Noah1989/loopmicro/software/collapseos/doc/hw/z80/rc2014/img/acia.jpg

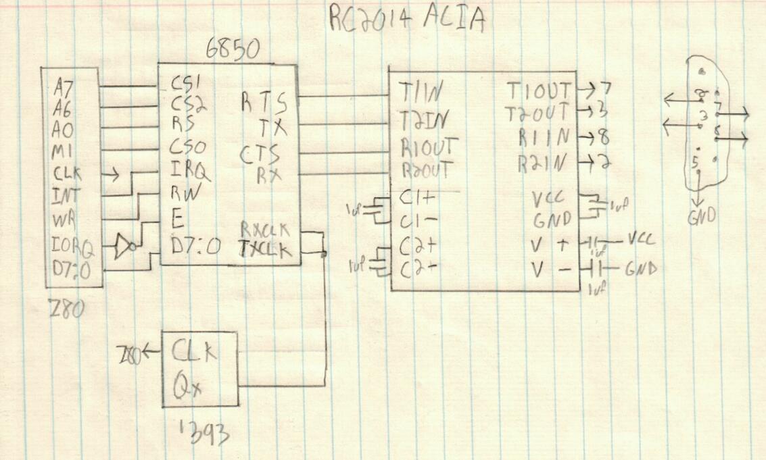
software/collapseos/doc/hw/z80/rc2014/img/acia.jpg
