Noah1989/loopmicro/memory/memory.kicad_pcb

## KiCad design memory/memory.kicad_pcb (2019-05-25)

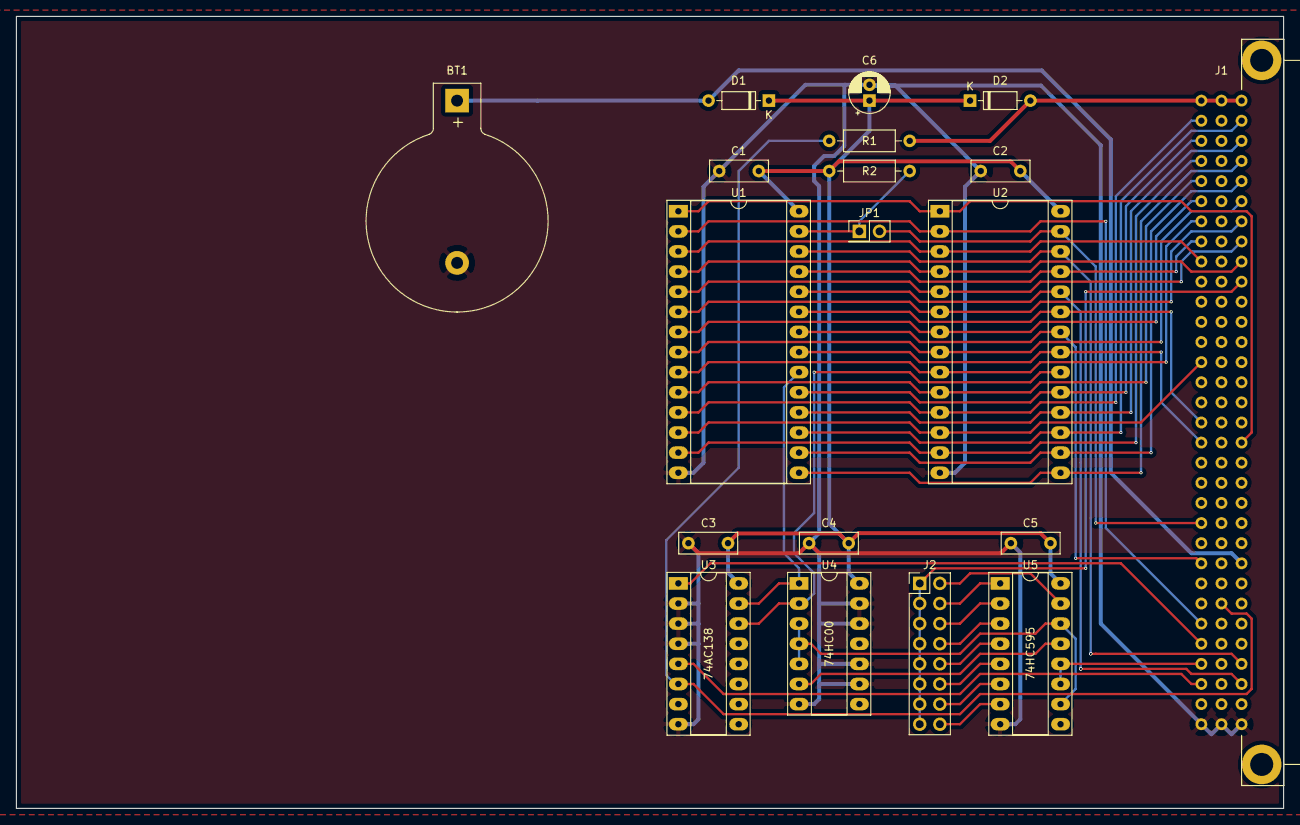
[picture p22: board memory.kicad_pcb from above]

Board: 2 copper layers, 160.0 x 100.0 mm, 19 parts (0 on the bottom side), 47 nets.

Parts:
BT1: Battery_Cell; BatteryHolder_Keystone_103_1x20mm
C1, C2, C3, C4, C5: C_Small; C_Rect_L7.2mm_W2.5mm_P5.00mm_FKS2_FKP2_MKS2_MKP2
C6: CP1; CP_Radial_D5.0mm_P2.00mm
D1, D2: D_ALT; D_DO-35_SOD27_P7.62mm_Horizontal
J1: C96ABC; Socket_DIN41612-CaseC1-full-Male-96Pin-3rows
J2: Conn_02x08_Odd_Even; PinHeader_2x08_P2.54mm_Vertical
JP1: Jumper; PinHeader_2x01_P2.54mm_Vertical
R1, R2: R; R_Axial_DIN0207_L6.3mm_D2.5mm_P10.16mm_Horizontal
U1, U2: LY62256PL-55LLI; DIP-28_W15.24mm_Socket_LongPads
U3: 74AC138; DIP-16_W7.62mm_Socket_LongPads
U4: 74HC00; DIP-14_W7.62mm_Socket_LongPads
U5: 74HC595; DIP-16_W7.62mm_Socket_LongPads

Connections:
+BATT: BT1.1, D1.2, J1.A24
A0: J1.C5, U1.10, U2.10
A1: J1.C7, U1.9, U2.9
A2: J1.A6, U1.8, U2.8
A3: J1.C6, U1.7, U2.7
A4: J1.A7, U1.6, U2.6
A5: J1.A8, U1.5, U2.5
A6: J1.A9, U1.4, U2.4
A7: J1.C9, U1.3, U2.3
A8: J1.C8, U1.25, U2.25
A9: J1.A30, U1.24, U2.24
A10: J1.C18, U1.21, U2.21
A11: J1.C17, U1.23, U2.23
A12: J1.C27, U1.2, U2.2
A13: J1.A29, U1.26, U2.26
A14: J1.A18, U1.1, U2.1
A15: J1.C28, U3.1
CLK: J1.C29, U5.11, U5.12
D0: J1.C2, U1.11, U2.11
D1: J1.C14, U1.12, U2.12
D2: J1.C4, U1.13, U2.13
D3: J1.A4, U1.15, U2.15
D4: J1.A5, U1.16, U2.16
D5: J1.A2, U1.17, U2.17
D6: J1.A3, U1.18, U2.18
D7: J1.C3, U1.19, U2.19
GND: BT1.2, C1.2, C2.2, C3.2, C4.2, C5.2, C6.2, J1.A32, J1.B32, J1.C32, U1.14, U2.14, U3.2, U3.3, U3.4, U3.8, U4.7, U4.9, U4.10, U4.12, U4.13, U5.8
unnamed: J2.2, U5.15
unnamed: J2.4, U5.1
unnamed: J2.6, U5.2
unnamed: J2.8, U5.3
unnamed: J2.10, U5.4
unnamed: J2.12, U5.5
unnamed: J2.14, U5.6
unnamed: J2.16, U5.7
unnamed: JP1.1, R2.2, U1.27
unnamed: U1.20, U3.15, U4.1
unnamed: U2.20, U3.14, U4.2
unnamed: U4.3, U4.4, U4.5, U5.10, U5.14
unnamed: U4.6, U5.13
VCC: D2.2, J1.A1, J1.B1, J1.C1, R1.2
VMEM: C1.1, C2.1, C3.1, C4.1, C5.1, C6.1, D1.1, D2.1, R2.1, U1.28, U2.28, U3.16, U4.14, U5.16
~MREQ: J1.C30, U3.5
~RD: J1.C24, U1.22, U2.22
~ROB: J1.B26, R1.1, U3.6
~WAIT: J1.A10, J2.1, J2.3, J2.5, J2.7, J2.9, J2.11, J2.13, J2.15
~WR: J1.C22, JP1.2, U2.27
