Noah1989/loopmicro/ledrom/ledrom.kicad_pcb

## KiCad design ledrom/ledrom.kicad_pcb (2019-05-25)

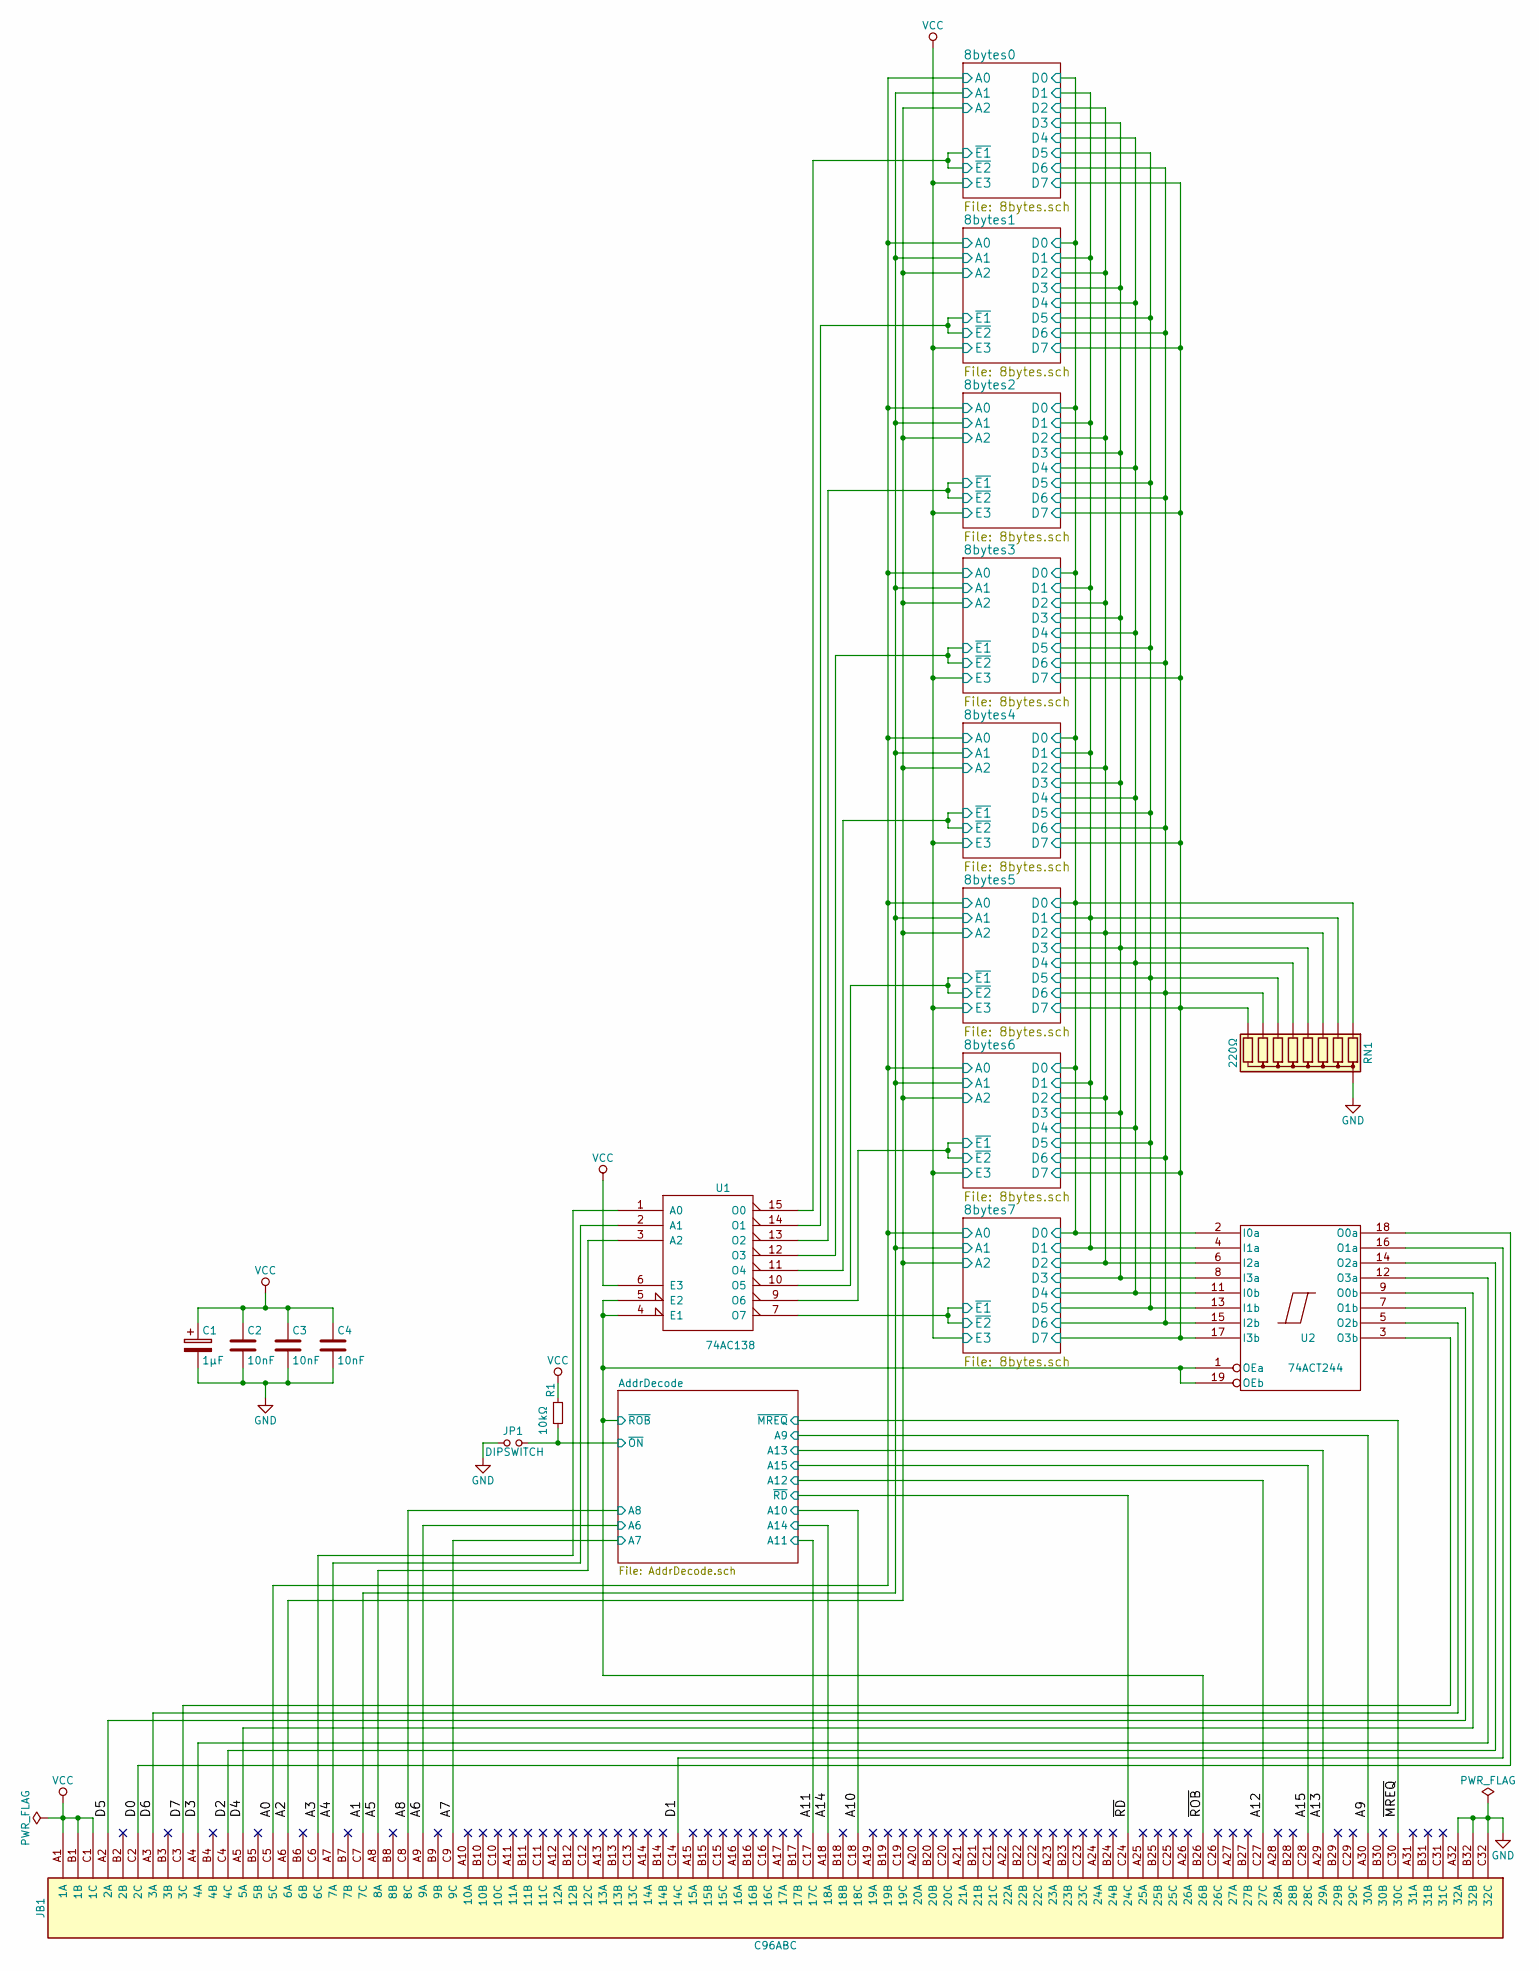
[picture p23: schematic ledrom.sch]

Parts:
C1: 1µF; CP_Radial_D5.0mm_P2.00mm
C2, C3, C4: 10nF; C_Rect_L7.0mm_W2.5mm_P5.00mm
JB1: C96ABC; Socket_DIN41612-CaseC1-full-Male-96Pin-3rows
JP1: DIPSWITCH; SW_DIP_x1_W7.62mm_Slide
R1: 10kΩ; R_Axial_DIN0207_L6.3mm_D2.5mm_P7.62mm_Horizontal
RN1: 220Ω; R_Array_SIP9
U1: 74AC138; DIP-16_W7.62mm_Socket
U2: 74ACT244; DIP-20_W7.62mm_Socket

Connections:
/8bytes0/D0: RN1.2 (R1), U2.2 (I0a); also elsewhere on the board
/8bytes0/D1: RN1.3 (R2), U2.4 (I1a); also elsewhere on the board
/8bytes0/D2: RN1.4 (R3), U2.6 (I2a); also elsewhere on the board
/8bytes0/D3: RN1.5 (R4), U2.8 (I3a); also elsewhere on the board
/8bytes0/D4: RN1.6 (R5), U2.11 (I0b); also elsewhere on the board
/8bytes0/D5: RN1.7 (R6), U2.13 (I1b); also elsewhere on the board
/8bytes0/D6: RN1.8 (R7), U2.15 (I2b); also elsewhere on the board
/8bytes0/D7: RN1.9 (R8), U2.17 (I3b); also elsewhere on the board
/8bytes0/~E1: U1.15 (O0); also elsewhere on the board
/8bytes1/~E1: U1.14 (O1); also elsewhere on the board
/8bytes2/~E1: U1.13 (O2); also elsewhere on the board
/8bytes3/~E1: U1.12 (O3); also elsewhere on the board
/8bytes4/~E1: U1.11 (O4); also elsewhere on the board
/8bytes5/~E1: U1.10 (O5); also elsewhere on the board
/8bytes6/~E1: U1.9 (O6); also elsewhere on the board
/8bytes7/~E1: U1.7 (O7); also elsewhere on the board
/A0: JB1.C5 (5C); also elsewhere on the board
/A1: JB1.C7 (7C); also elsewhere on the board
/A2: JB1.A6 (6A); also elsewhere on the board
/A3: JB1.C6 (6C), U1.1 (A0)
/A4: JB1.A7 (7A), U1.2 (A1)
/A5: JB1.A8 (8A), U1.3 (A2)
/A6: JB1.A9 (9A); also elsewhere on the board
/A7: JB1.C9 (9C); also elsewhere on the board
/A8: JB1.C8 (8C); also elsewhere on the board
/A9: JB1.A30 (30A); also elsewhere on the board
/A10: JB1.C18 (18C); also elsewhere on the board
/A11: JB1.C17 (17C); also elsewhere on the board
/A12: JB1.C27 (27C); also elsewhere on the board
/A13: JB1.A29 (29A); also elsewhere on the board
/A14: JB1.A18 (18A); also elsewhere on the board
/A15: JB1.C28 (28C); also elsewhere on the board
/AddrDecode/~ON: JP1.2, R1.2; also elsewhere on the board
/D0: JB1.C2 (2C), U2.18 (O0a)
/D1: JB1.C14 (14C), U2.16 (O1a)
/D2: JB1.C4 (4C), U2.14 (O2a)
/D3: JB1.A4 (4A), U2.12 (O3a)
/D4: JB1.A5 (5A), U2.9 (O0b)
/D5: JB1.A2 (2A), U2.7 (O1b)
/D6: JB1.A3 (3A), U2.5 (O2b)
/D7: JB1.C3 (3C), U2.3 (O3b)
/~MREQ: JB1.C30 (30C); also elsewhere on the board
/~RD: JB1.C24 (24C); also elsewhere on the board
/~ROB: JB1.B26 (26B), U1.4 (E1), U1.5 (E2), U2.1 (OEa), U2.19 (OEb); also elsewhere on the board
GND: C1.2, C2.2, C3.2, C4.2, JB1.A32 (32A), JB1.B32 (32B), JB1.C32 (32C), JP1.1, RN1.1 (common), U1.8 (GND), U2.10 (GND); also elsewhere on the board
VCC: C1.1, C2.1, C3.1, C4.1, JB1.A1 (1A), JB1.B1 (1B), JB1.C1 (1C), R1.1, U1.6 (E3), U1.16 (VCC), U2.20 (VCC); also elsewhere on the board

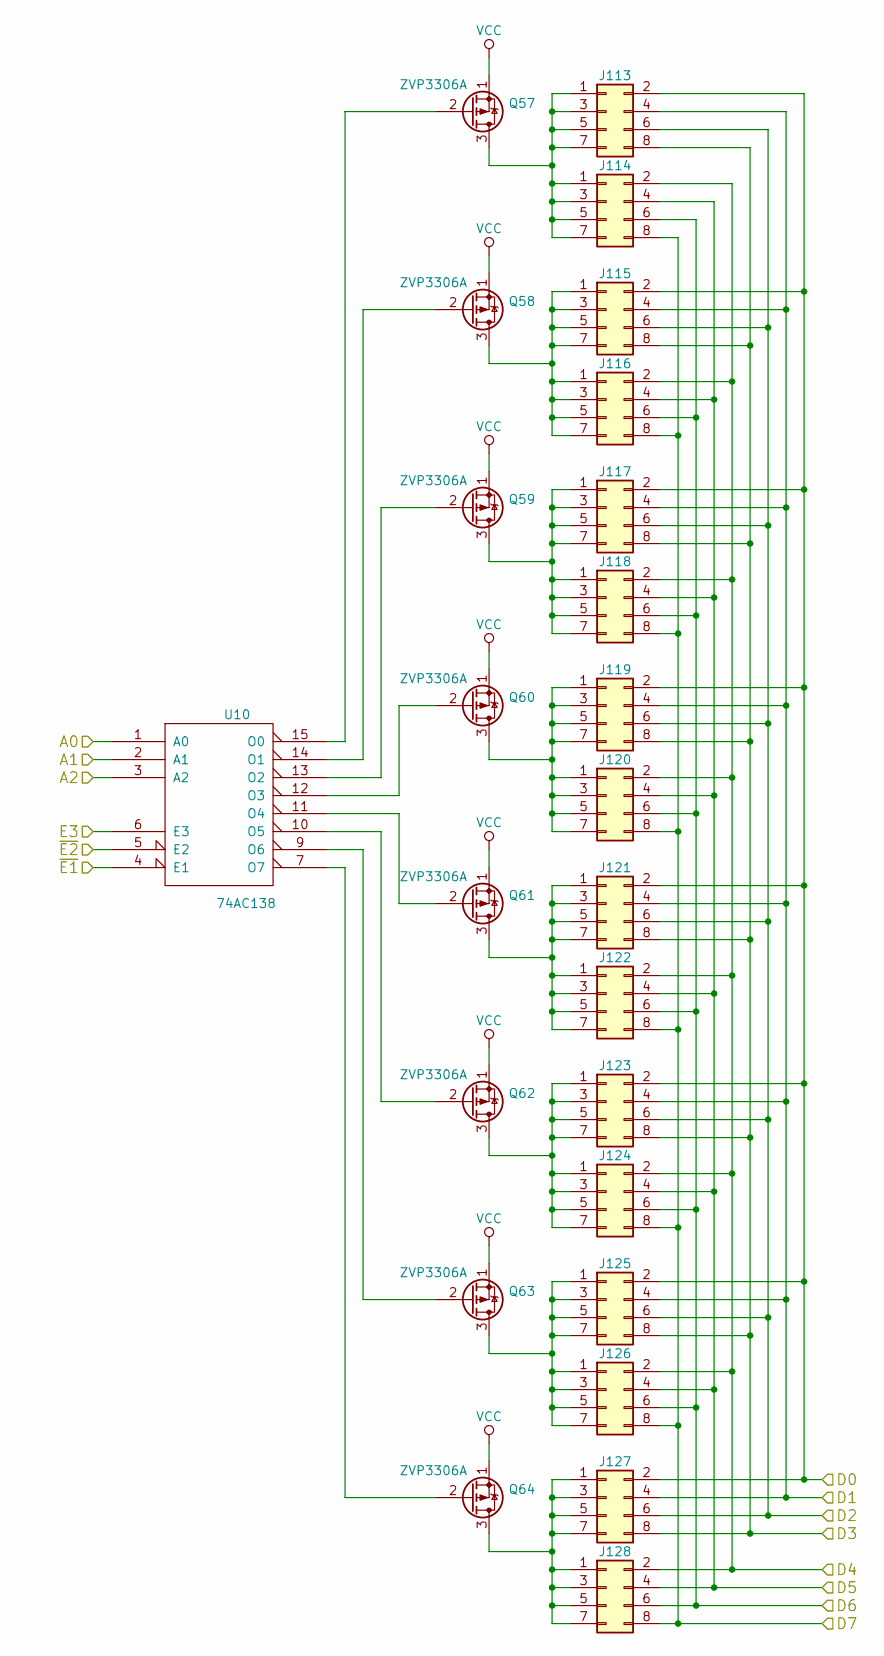
[picture p24: schematic 8bytes.sch]

Parts:
J1, J2, J3, J4, J5, J6, J7, J8, J9, J10, J11, J12, J13, J14, J15, J16: Conn_02x04_Odd_Even; Socket_Strip_Straight_2x04_Pitch2.54mm
Q1, Q2, Q3, Q4, Q5, Q6, Q7, Q8: ZVP3306A; TO-92_Inline_Narrow_Oval
U3: 74AC138; DIP-16_W7.62mm_Socket

Connections:
/8bytes0/D0: J1.2, J3.2, J5.2, J7.2, J9.2, J11.2, J13.2, J15.2; also elsewhere on the board
/8bytes0/D1: J1.4, J3.4, J5.4, J7.4, J9.4, J11.4, J13.4, J15.4; also elsewhere on the board
/8bytes0/D2: J1.6, J3.6, J5.6, J7.6, J9.6, J11.6, J13.6, J15.6; also elsewhere on the board
/8bytes0/D3: J1.8, J3.8, J5.8, J7.8, J9.8, J11.8, J13.8, J15.8; also elsewhere on the board
/8bytes0/D4: J2.2, J4.2, J6.2, J8.2, J10.2, J12.2, J14.2, J16.2; also elsewhere on the board
/8bytes0/D5: J2.4, J4.4, J6.4, J8.4, J10.4, J12.4, J14.4, J16.4; also elsewhere on the board
/8bytes0/D6: J2.6, J4.6, J6.6, J8.6, J10.6, J12.6, J14.6, J16.6; also elsewhere on the board
/8bytes0/D7: J2.8, J4.8, J6.8, J8.8, J10.8, J12.8, J14.8, J16.8; also elsewhere on the board
/8bytes0/~E1: U3.4 (E1), U3.5 (E2); also elsewhere on the board
/A0: U3.1 (A0); also elsewhere on the board
/A1: U3.2 (A1); also elsewhere on the board
/A2: U3.3 (A2); also elsewhere on the board
GND: U3.8 (GND); also elsewhere on the board
unnamed: J1.1, J1.3, J1.5, J1.7, J2.1, J2.3, J2.5, J2.7, Q1.3 (D)
unnamed: J3.1, J3.3, J3.5, J3.7, J4.1, J4.3, J4.5, J4.7, Q2.3 (D)
unnamed: J5.1, J5.3, J5.5, J5.7, J6.1, J6.3, J6.5, J6.7, Q3.3 (D)
unnamed: J7.1, J7.3, J7.5, J7.7, J8.1, J8.3, J8.5, J8.7, Q4.3 (D)
unnamed: J9.1, J9.3, J9.5, J9.7, J10.1, J10.3, J10.5, J10.7, Q5.3 (D)
unnamed: J11.1, J11.3, J11.5, J11.7, J12.1, J12.3, J12.5, J12.7, Q6.3 (D)
unnamed: J13.1, J13.3, J13.5, J13.7, J14.1, J14.3, J14.5, J14.7, Q7.3 (D)
unnamed: J15.1, J15.3, J15.5, J15.7, J16.1, J16.3, J16.5, J16.7, Q8.3 (D)
unnamed: Q1.2 (G), U3.15 (O0)
unnamed: Q2.2 (G), U3.14 (O1)
unnamed: Q3.2 (G), U3.13 (O2)
unnamed: Q4.2 (G), U3.12 (O3)
unnamed: Q5.2 (G), U3.11 (O4)
unnamed: Q6.2 (G), U3.10 (O5)
unnamed: Q7.2 (G), U3.9 (O6)
unnamed: Q8.2 (G), U3.7 (O7)
VCC: Q1.1 (S), Q2.1 (S), Q3.1 (S), Q4.1 (S), Q5.1 (S), Q6.1 (S), Q7.1 (S), Q8.1 (S), U3.6 (E3), U3.16 (VCC); also elsewhere on the board

Parts of its further copies:
J17, J18, J19, J20, J21, J22, J23, J24, J25, J26, J27, J28, J29, J30, J31, J32, J33, J34, J35, J36, J37, J38, J39, J40, J41, J42, J43, J44, J45, J46, J47, J48, J49, J50, J51, J52, J53, J54, J55, J56, J57, J58, J59, J60, J61, J62, J63, J64, J65, J66, J67, J68, J69, J70, J71, J72, J73, J74, J75, J76, J77, J78, J79, J80, J81, J82, J83, J84, J85, J86, J87, J88, J89, J90, J91, J92, J93, J94, J95, J96, J97, J98, J99, J100, J101, J102, J103, J104, J105, J106, J107, J108, J109, J110, J111, J112, J113, J114, J115, J116, J117, J118, J119, J120, J121, J122, J123, J124, J125, J126, J127, J128: Conn_02x04_Odd_Even; Socket_Strip_Straight_2x04_Pitch2.54mm
Q9, Q10, Q11, Q12, Q13, Q14, Q15, Q16, Q17, Q18, Q19, Q20, Q21, Q22, Q23, Q24, Q25, Q26, Q27, Q28, Q29, Q30, Q31, Q32, Q33, Q34, Q35, Q36, Q37, Q38, Q39, Q40, Q41, Q42, Q43, Q44, Q45, Q46, Q47, Q48, Q49, Q50, Q51, Q52, Q53, Q54, Q55, Q56, Q57, Q58, Q59, Q60, Q61, Q62, Q63, Q64: ZVP3306A; TO-92_Inline_Narrow_Oval
U4, U5, U6, U7, U8, U9, U10: 74AC138; DIP-16_W7.62mm_Socket

Connections of its further copies:
/8bytes0/D0: J17.2, J19.2, J21.2, J23.2, J25.2, J27.2, J29.2, J31.2, J33.2, J35.2, J37.2, J39.2, J41.2, J43.2, J45.2, J47.2, J49.2, J51.2, J53.2, J55.2, J57.2, J59.2, J61.2, J63.2, J65.2, J67.2, J69.2, J71.2, J73.2, J75.2, J77.2, J79.2, J81.2, J83.2, J85.2, J87.2, J89.2, J91.2, J93.2, J95.2, J97.2, J99.2, J101.2, J103.2, J105.2, J107.2, J109.2, J111.2, J113.2, J115.2, J117.2, J119.2, J121.2, J123.2, J125.2, J127.2; also elsewhere on the board
/8bytes0/D1: J17.4, J19.4, J21.4, J23.4, J25.4, J27.4, J29.4, J31.4, J33.4, J35.4, J37.4, J39.4, J41.4, J43.4, J45.4, J47.4, J49.4, J51.4, J53.4, J55.4, J57.4, J59.4, J61.4, J63.4, J65.4, J67.4, J69.4, J71.4, J73.4, J75.4, J77.4, J79.4, J81.4, J83.4, J85.4, J87.4, J89.4, J91.4, J93.4, J95.4, J97.4, J99.4, J101.4, J103.4, J105.4, J107.4, J109.4, J111.4, J113.4, J115.4, J117.4, J119.4, J121.4, J123.4, J125.4, J127.4; also elsewhere on the board
/8bytes0/D2: J17.6, J19.6, J21.6, J23.6, J25.6, J27.6, J29.6, J31.6, J33.6, J35.6, J37.6, J39.6, J41.6, J43.6, J45.6, J47.6, J49.6, J51.6, J53.6, J55.6, J57.6, J59.6, J61.6, J63.6, J65.6, J67.6, J69.6, J71.6, J73.6, J75.6, J77.6, J79.6, J81.6, J83.6, J85.6, J87.6, J89.6, J91.6, J93.6, J95.6, J97.6, J99.6, J101.6, J103.6, J105.6, J107.6, J109.6, J111.6, J113.6, J115.6, J117.6, J119.6, J121.6, J123.6, J125.6, J127.6; also elsewhere on the board
/8bytes0/D3: J17.8, J19.8, J21.8, J23.8, J25.8, J27.8, J29.8, J31.8, J33.8, J35.8, J37.8, J39.8, J41.8, J43.8, J45.8, J47.8, J49.8, J51.8, J53.8, J55.8, J57.8, J59.8, J61.8, J63.8, J65.8, J67.8, J69.8, J71.8, J73.8, J75.8, J77.8, J79.8, J81.8, J83.8, J85.8, J87.8, J89.8, J91.8, J93.8, J95.8, J97.8, J99.8, J101.8, J103.8, J105.8, J107.8, J109.8, J111.8, J113.8, J115.8, J117.8, J119.8, J121.8, J123.8, J125.8, J127.8; also elsewhere on the board
/8bytes0/D4: J18.2, J20.2, J22.2, J24.2, J26.2, J28.2, J30.2, J32.2, J34.2, J36.2, J38.2, J40.2, J42.2, J44.2, J46.2, J48.2, J50.2, J52.2, J54.2, J56.2, J58.2, J60.2, J62.2, J64.2, J66.2, J68.2, J70.2, J72.2, J74.2, J76.2, J78.2, J80.2, J82.2, J84.2, J86.2, J88.2, J90.2, J92.2, J94.2, J96.2, J98.2, J100.2, J102.2, J104.2, J106.2, J108.2, J110.2, J112.2, J114.2, J116.2, J118.2, J120.2, J122.2, J124.2, J126.2, J128.2; also elsewhere on the board
/8bytes0/D5: J18.4, J20.4, J22.4, J24.4, J26.4, J28.4, J30.4, J32.4, J34.4, J36.4, J38.4, J40.4, J42.4, J44.4, J46.4, J48.4, J50.4, J52.4, J54.4, J56.4, J58.4, J60.4, J62.4, J64.4, J66.4, J68.4, J70.4, J72.4, J74.4, J76.4, J78.4, J80.4, J82.4, J84.4, J86.4, J88.4, J90.4, J92.4, J94.4, J96.4, J98.4, J100.4, J102.4, J104.4, J106.4, J108.4, J110.4, J112.4, J114.4, J116.4, J118.4, J120.4, J122.4, J124.4, J126.4, J128.4; also elsewhere on the board
/8bytes0/D6: J18.6, J20.6, J22.6, J24.6, J26.6, J28.6, J30.6, J32.6, J34.6, J36.6, J38.6, J40.6, J42.6, J44.6, J46.6, J48.6, J50.6, J52.6, J54.6, J56.6, J58.6, J60.6, J62.6, J64.6, J66.6, J68.6, J70.6, J72.6, J74.6, J76.6, J78.6, J80.6, J82.6, J84.6, J86.6, J88.6, J90.6, J92.6, J94.6, J96.6, J98.6, J100.6, J102.6, J104.6, J106.6, J108.6, J110.6, J112.6, J114.6, J116.6, J118.6, J120.6, J122.6, J124.6, J126.6, J128.6; also elsewhere on the board
/8bytes0/D7: J18.8, J20.8, J22.8, J24.8, J26.8, J28.8, J30.8, J32.8, J34.8, J36.8, J38.8, J40.8, J42.8, J44.8, J46.8, J48.8, J50.8, J52.8, J54.8, J56.8, J58.8, J60.8, J62.8, J64.8, J66.8, J68.8, J70.8, J72.8, J74.8, J76.8, J78.8, J80.8, J82.8, J84.8, J86.8, J88.8, J90.8, J92.8, J94.8, J96.8, J98.8, J100.8, J102.8, J104.8, J106.8, J108.8, J110.8, J112.8, J114.8, J116.8, J118.8, J120.8, J122.8, J124.8, J126.8, J128.8; also elsewhere on the board
/8bytes1/~E1: U4.4 (E1), U4.5 (E2); also elsewhere on the board
/8bytes2/~E1: U5.4 (E1), U5.5 (E2); also elsewhere on the board
/8bytes3/~E1: U6.4 (E1), U6.5 (E2); also elsewhere on the board
/8bytes4/~E1: U7.4 (E1), U7.5 (E2); also elsewhere on the board
/8bytes5/~E1: U8.4 (E1), U8.5 (E2); also elsewhere on the board
/8bytes6/~E1: U9.4 (E1), U9.5 (E2); also elsewhere on the board
/8bytes7/~E1: U10.4 (E1), U10.5 (E2); also elsewhere on the board
/A0: U4.1 (A0), U5.1 (A0), U6.1 (A0), U7.1 (A0), U8.1 (A0), U9.1 (A0), U10.1 (A0); also elsewhere on the board
/A1: U4.2 (A1), U5.2 (A1), U6.2 (A1), U7.2 (A1), U8.2 (A1), U9.2 (A1), U10.2 (A1); also elsewhere on the board
/A2: U4.3 (A2), U5.3 (A2), U6.3 (A2), U7.3 (A2), U8.3 (A2), U9.3 (A2), U10.3 (A2); also elsewhere on the board
GND: U4.8 (GND), U5.8 (GND), U6.8 (GND), U7.8 (GND), U8.8 (GND), U9.8 (GND), U10.8 (GND); also elsewhere on the board
unnamed: J17.1, J17.3, J17.5, J17.7, J18.1, J18.3, J18.5, J18.7, Q9.3 (D)
unnamed: J19.1, J19.3, J19.5, J19.7, J20.1, J20.3, J20.5, J20.7, Q10.3 (D)
unnamed: J21.1, J21.3, J21.5, J21.7, J22.1, J22.3, J22.5, J22.7, Q11.3 (D)
unnamed: J23.1, J23.3, J23.5, J23.7, J24.1, J24.3, J24.5, J24.7, Q12.3 (D)
unnamed: J25.1, J25.3, J25.5, J25.7, J26.1, J26.3, J26.5, J26.7, Q13.3 (D)
unnamed: J27.1, J27.3, J27.5, J27.7, J28.1, J28.3, J28.5, J28.7, Q14.3 (D)
unnamed: J29.1, J29.3, J29.5, J29.7, J30.1, J30.3, J30.5, J30.7, Q15.3 (D)
unnamed: J31.1, J31.3, J31.5, J31.7, J32.1, J32.3, J32.5, J32.7, Q16.3 (D)
unnamed: J33.1, J33.3, J33.5, J33.7, J34.1, J34.3, J34.5, J34.7, Q17.3 (D)
unnamed: J35.1, J35.3, J35.5, J35.7, J36.1, J36.3, J36.5, J36.7, Q18.3 (D)
unnamed: J37.1, J37.3, J37.5, J37.7, J38.1, J38.3, J38.5, J38.7, Q19.3 (D)
unnamed: J39.1, J39.3, J39.5, J39.7, J40.1, J40.3, J40.5, J40.7, Q20.3 (D)
unnamed: J41.1, J41.3, J41.5, J41.7, J42.1, J42.3, J42.5, J42.7, Q21.3 (D)
unnamed: J43.1, J43.3, J43.5, J43.7, J44.1, J44.3, J44.5, J44.7, Q22.3 (D)
unnamed: J45.1, J45.3, J45.5, J45.7, J46.1, J46.3, J46.5, J46.7, Q23.3 (D)
unnamed: J47.1, J47.3, J47.5, J47.7, J48.1, J48.3, J48.5, J48.7, Q24.3 (D)
unnamed: J49.1, J49.3, J49.5, J49.7, J50.1, J50.3, J50.5, J50.7, Q25.3 (D)
unnamed: J51.1, J51.3, J51.5, J51.7, J52.1, J52.3, J52.5, J52.7, Q26.3 (D)
unnamed: J53.1, J53.3, J53.5, J53.7, J54.1, J54.3, J54.5, J54.7, Q27.3 (D)
unnamed: J55.1, J55.3, J55.5, J55.7, J56.1, J56.3, J56.5, J56.7, Q28.3 (D)
unnamed: J57.1, J57.3, J57.5, J57.7, J58.1, J58.3, J58.5, J58.7, Q29.3 (D)
unnamed: J59.1, J59.3, J59.5, J59.7, J60.1, J60.3, J60.5, J60.7, Q30.3 (D)
unnamed: J61.1, J61.3, J61.5, J61.7, J62.1, J62.3, J62.5, J62.7, Q31.3 (D)
unnamed: J63.1, J63.3, J63.5, J63.7, J64.1, J64.3, J64.5, J64.7, Q32.3 (D)
unnamed: J65.1, J65.3, J65.5, J65.7, J66.1, J66.3, J66.5, J66.7, Q33.3 (D)
unnamed: J67.1, J67.3, J67.5, J67.7, J68.1, J68.3, J68.5, J68.7, Q34.3 (D)
unnamed: J69.1, J69.3, J69.5, J69.7, J70.1, J70.3, J70.5, J70.7, Q35.3 (D)
unnamed: J71.1, J71.3, J71.5, J71.7, J72.1, J72.3, J72.5, J72.7, Q36.3 (D)
unnamed: J73.1, J73.3, J73.5, J73.7, J74.1, J74.3, J74.5, J74.7, Q37.3 (D)
unnamed: J75.1, J75.3, J75.5, J75.7, J76.1, J76.3, J76.5, J76.7, Q38.3 (D)
unnamed: J77.1, J77.3, J77.5, J77.7, J78.1, J78.3, J78.5, J78.7, Q39.3 (D)
unnamed: J79.1, J79.3, J79.5, J79.7, J80.1, J80.3, J80.5, J80.7, Q40.3 (D)
unnamed: J81.1, J81.3, J81.5, J81.7, J82.1, J82.3, J82.5, J82.7, Q41.3 (D)
unnamed: J83.1, J83.3, J83.5, J83.7, J84.1, J84.3, J84.5, J84.7, Q42.3 (D)
unnamed: J85.1, J85.3, J85.5, J85.7, J86.1, J86.3, J86.5, J86.7, Q43.3 (D)
unnamed: J87.1, J87.3, J87.5, J87.7, J88.1, J88.3, J88.5, J88.7, Q44.3 (D)
unnamed: J89.1, J89.3, J89.5, J89.7, J90.1, J90.3, J90.5, J90.7, Q45.3 (D)
unnamed: J91.1, J91.3, J91.5, J91.7, J92.1, J92.3, J92.5, J92.7, Q46.3 (D)
unnamed: J93.1, J93.3, J93.5, J93.7, J94.1, J94.3, J94.5, J94.7, Q47.3 (D)
unnamed: J95.1, J95.3, J95.5, J95.7, J96.1, J96.3, J96.5, J96.7, Q48.3 (D)
unnamed: J97.1, J97.3, J97.5, J97.7, J98.1, J98.3, J98.5, J98.7, Q49.3 (D)
unnamed: J99.1, J99.3, J99.5, J99.7, J100.1, J100.3, J100.5, J100.7, Q50.3 (D)
unnamed: J101.1, J101.3, J101.5, J101.7, J102.1, J102.3, J102.5, J102.7, Q51.3 (D)
unnamed: J103.1, J103.3, J103.5, J103.7, J104.1, J104.3, J104.5, J104.7, Q52.3 (D)
unnamed: J105.1, J105.3, J105.5, J105.7, J106.1, J106.3, J106.5, J106.7, Q53.3 (D)
unnamed: J107.1, J107.3, J107.5, J107.7, J108.1, J108.3, J108.5, J108.7, Q54.3 (D)
unnamed: J109.1, J109.3, J109.5, J109.7, J110.1, J110.3, J110.5, J110.7, Q55.3 (D)
unnamed: J111.1, J111.3, J111.5, J111.7, J112.1, J112.3, J112.5, J112.7, Q56.3 (D)
unnamed: J113.1, J113.3, J113.5, J113.7, J114.1, J114.3, J114.5, J114.7, Q57.3 (D)
unnamed: J115.1, J115.3, J115.5, J115.7, J116.1, J116.3, J116.5, J116.7, Q58.3 (D)
unnamed: J117.1, J117.3, J117.5, J117.7, J118.1, J118.3, J118.5, J118.7, Q59.3 (D)
unnamed: J119.1, J119.3, J119.5, J119.7, J120.1, J120.3, J120.5, J120.7, Q60.3 (D)
unnamed: J121.1, J121.3, J121.5, J121.7, J122.1, J122.3, J122.5, J122.7, Q61.3 (D)
unnamed: J123.1, J123.3, J123.5, J123.7, J124.1, J124.3, J124.5, J124.7, Q62.3 (D)
unnamed: J125.1, J125.3, J125.5, J125.7, J126.1, J126.3, J126.5, J126.7, Q63.3 (D)
unnamed: J127.1, J127.3, J127.5, J127.7, J128.1, J128.3, J128.5, J128.7, Q64.3 (D)
unnamed: Q9.2 (G), U4.15 (O0)
unnamed: Q10.2 (G), U4.14 (O1)
unnamed: Q11.2 (G), U4.13 (O2)
unnamed: Q12.2 (G), U4.12 (O3)
unnamed: Q13.2 (G), U4.11 (O4)
unnamed: Q14.2 (G), U4.10 (O5)
unnamed: Q15.2 (G), U4.9 (O6)
unnamed: Q16.2 (G), U4.7 (O7)
unnamed: Q17.2 (G), U5.15 (O0)
unnamed: Q18.2 (G), U5.14 (O1)
unnamed: Q19.2 (G), U5.13 (O2)
unnamed: Q20.2 (G), U5.12 (O3)
unnamed: Q21.2 (G), U5.11 (O4)
unnamed: Q22.2 (G), U5.10 (O5)
unnamed: Q23.2 (G), U5.9 (O6)
unnamed: Q24.2 (G), U5.7 (O7)
unnamed: Q25.2 (G), U6.15 (O0)
unnamed: Q26.2 (G), U6.14 (O1)
unnamed: Q27.2 (G), U6.13 (O2)
unnamed: Q28.2 (G), U6.12 (O3)
unnamed: Q29.2 (G), U6.11 (O4)
unnamed: Q30.2 (G), U6.10 (O5)
unnamed: Q31.2 (G), U6.9 (O6)
unnamed: Q32.2 (G), U6.7 (O7)
unnamed: Q33.2 (G), U7.15 (O0)
unnamed: Q34.2 (G), U7.14 (O1)
unnamed: Q35.2 (G), U7.13 (O2)
unnamed: Q36.2 (G), U7.12 (O3)
unnamed: Q37.2 (G), U7.11 (O4)
unnamed: Q38.2 (G), U7.10 (O5)
unnamed: Q39.2 (G), U7.9 (O6)
unnamed: Q40.2 (G), U7.7 (O7)
unnamed: Q41.2 (G), U8.15 (O0)
unnamed: Q42.2 (G), U8.14 (O1)
unnamed: Q43.2 (G), U8.13 (O2)
unnamed: Q44.2 (G), U8.12 (O3)
unnamed: Q45.2 (G), U8.11 (O4)
unnamed: Q46.2 (G), U8.10 (O5)
unnamed: Q47.2 (G), U8.9 (O6)
unnamed: Q48.2 (G), U8.7 (O7)
unnamed: Q49.2 (G), U9.15 (O0)
unnamed: Q50.2 (G), U9.14 (O1)
unnamed: Q51.2 (G), U9.13 (O2)
unnamed: Q52.2 (G), U9.12 (O3)
unnamed: Q53.2 (G), U9.11 (O4)
unnamed: Q54.2 (G), U9.10 (O5)
unnamed: Q55.2 (G), U9.9 (O6)
unnamed: Q56.2 (G), U9.7 (O7)
unnamed: Q57.2 (G), U10.15 (O0)
unnamed: Q58.2 (G), U10.14 (O1)
unnamed: Q59.2 (G), U10.13 (O2)
unnamed: Q60.2 (G), U10.12 (O3)
unnamed: Q61.2 (G), U10.11 (O4)
unnamed: Q62.2 (G), U10.10 (O5)
unnamed: Q63.2 (G), U10.9 (O6)
unnamed: Q64.2 (G), U10.7 (O7)
VCC: Q9.1 (S), Q10.1 (S), Q11.1 (S), Q12.1 (S), Q13.1 (S), Q14.1 (S), Q15.1 (S), Q16.1 (S), Q17.1 (S), Q18.1 (S), Q19.1 (S), Q20.1 (S), Q21.1 (S), Q22.1 (S), Q23.1 (S), Q24.1 (S), Q25.1 (S), Q26.1 (S), Q27.1 (S), Q28.1 (S), Q29.1 (S), Q30.1 (S), Q31.1 (S), Q32.1 (S), Q33.1 (S), Q34.1 (S), Q35.1 (S), Q36.1 (S), Q37.1 (S), Q38.1 (S), Q39.1 (S), Q40.1 (S), Q41.1 (S), Q42.1 (S), Q43.1 (S), Q44.1 (S), Q45.1 (S), Q46.1 (S), Q47.1 (S), Q48.1 (S), Q49.1 (S), Q50.1 (S), Q51.1 (S), Q52.1 (S), Q53.1 (S), Q54.1 (S), Q55.1 (S), Q56.1 (S), Q57.1 (S), Q58.1 (S), Q59.1 (S), Q60.1 (S), Q61.1 (S), Q62.1 (S), Q63.1 (S), Q64.1 (S), U4.6 (E3), U4.16 (VCC), U5.6 (E3), U5.16 (VCC), U6.6 (E3), U6.16 (VCC), U7.6 (E3), U7.16 (VCC), U8.6 (E3), U8.16 (VCC), U9.6 (E3), U9.16 (VCC), U10.6 (E3), U10.16 (VCC); also elsewhere on the board

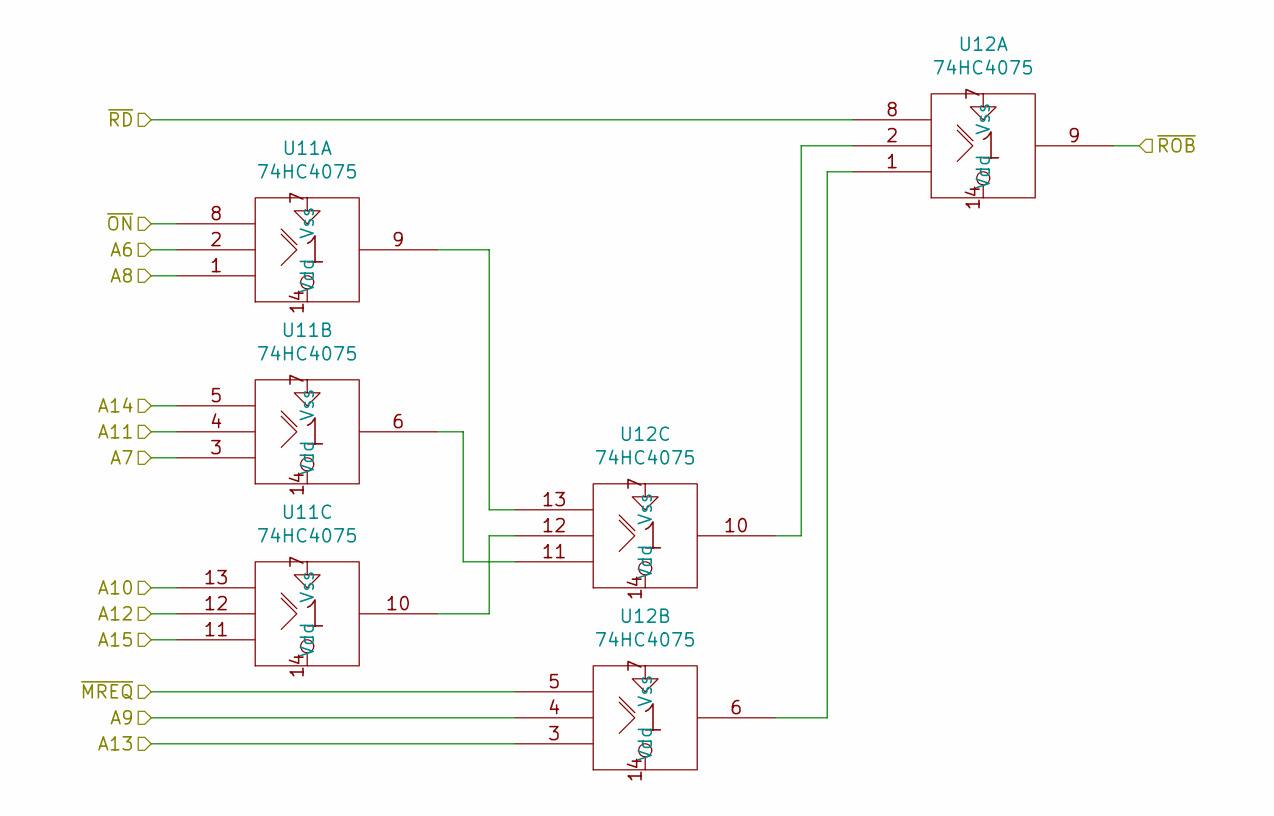
[picture p25: schematic AddrDecode.sch]

Parts:
U11, U12: 74HC4075; DIP-14_W7.62mm_Socket

Connections:
/A6: U11.2; also elsewhere on the board
/A7: U11.3; also elsewhere on the board
/A8: U11.1; also elsewhere on the board
/A9: U12.4; also elsewhere on the board
/A10: U11.13; also elsewhere on the board
/A11: U11.4; also elsewhere on the board
/A12: U11.12; also elsewhere on the board
/A13: U12.3; also elsewhere on the board
/A14: U11.5; also elsewhere on the board
/A15: U11.11; also elsewhere on the board
/AddrDecode/~ON: U11.8; also elsewhere on the board
/~MREQ: U12.5; also elsewhere on the board
/~RD: U12.8; also elsewhere on the board
/~ROB: U12.9; also elsewhere on the board
GND: U11.7 (Vss), U12.7 (Vss); also elsewhere on the board
unnamed: U11.6, U12.11
unnamed: U11.9, U12.13
unnamed: U11.10, U12.12
unnamed: U12.1, U12.6
unnamed: U12.2, U12.10
VCC: U11.14 (Vdd), U12.14 (Vdd); also elsewhere on the board

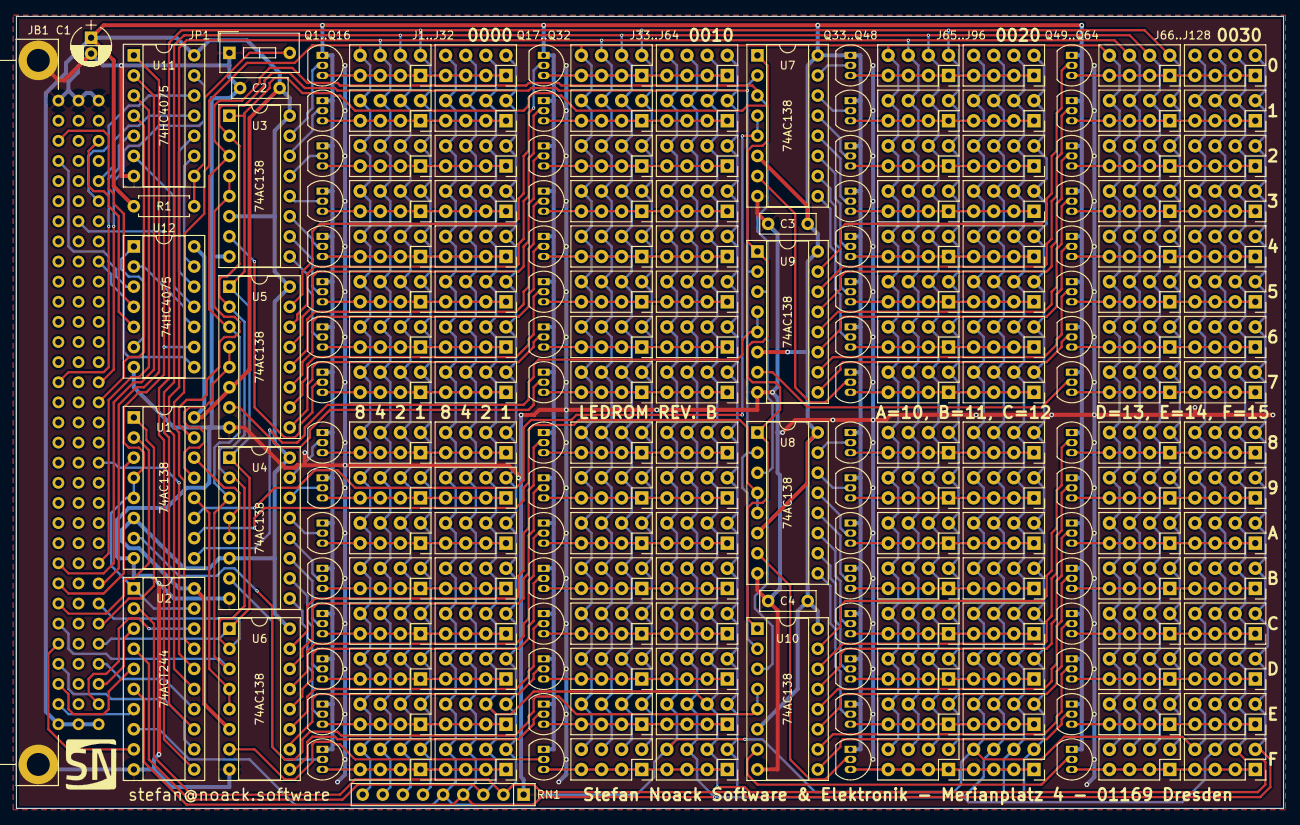
[picture p26: board ledrom.kicad_pcb from above]

Board: 2 copper layers, 160.0 x 100.0 mm, 212 parts (0 on the bottom side), 179 nets.
