Noah1989/loopmicro/software/new-rom/fat32.asm

public fat32_init
public fat32_working_directory
public fat32_fat_begin_lba
public fat32_fat_number_of_sectors
public fat32_chain_IX_get_byte_A
public fat32_chain_IX_put_byte_A
public fat32_chain_IX_skip_bytes_BC
public fat32_chain_IX_seek_BCDE


extern sdcard_read_block_DEHL_lazy
extern sdcard_block_buffer
extern sdcard_current_block_address
extern sdcard_current_block_dirty

extern stream_IX_seek_BCDE
extern stream_IX_read_block_DE_len_BC_bytewise
extern stream_IX_write_block_DE_len_BC_bytewise

extern debug_io_print_character_A
extern debug_io_print_hex_byte_A
extern error

include "stream.inc"
include "fat32.inc"

defc volumeid_bytes_per_sector      = $00B ; ds.b 2
defc volumeid_sectors_per_cluster   = $00D ; ds.b 1
defc volumeid_reserved_sectors      = $00E ; ds.b 2
defc volumeid_number_of_fats        = $010 ; ds.b 1
defc volumeid_sectors_per_fat       = $024 ; ds.b 4
defc volumeid_rootdir_first_cluster = $02C ; ds.b 4
defc volumeid_signature             = $1FE ; ds.b 2

fat32_init:
	; read master boot record
	LD	DE, 0
	LD	HL, 0
	CALL	sdcard_read_block_DEHL_lazy
	; verify this is a dos mbr
	LD	HL, (sdcard_block_buffer+mbr_magic)
	LD	BC, $AA55
	AND	A, A
	SBC	HL, BC
fat32_init_error_invalid_mbr_signature:
	CALL	NZ, error
	; verify filesystem type is $0B or $0C (FAT32)
	LD	A, (sdcard_block_buffer+mbr_partition_1+partition_type_code)
	CP	A, $0B
	JR	Z, fat32_init_type_ok
	CP	A, $0C
fat32_init_error_invalid_fs_type:
	CALL	NZ, error
fat32_init_type_ok:
	; read volume id
	LD	HL, (sdcard_block_buffer+mbr_partition_1+partition_lba_begin)
	LD	DE, (sdcard_block_buffer+mbr_partition_1+partition_lba_begin+2)
	CALL	sdcard_read_block_DEHL_lazy
	; check signature
	LD	HL, (sdcard_block_buffer+volumeid_signature)
	LD	BC, $AA55
	AND	A, A
	SBC	HL, BC
fat32_init_error_invalid_volumeid_signature:
	CALL	NZ, error
	; check bytes per sector
	LD	HL, (sdcard_block_buffer+volumeid_bytes_per_sector)
	LD	BC, 512
	AND	A, A
	SBC	HL, BC
fat32_init_error_invalid_sector_size:
	CALL	NZ, error
	; check number of FATs
	LD	A, (sdcard_block_buffer+volumeid_number_of_fats)
	CP	A, 2
fat32_init_error_invalid_number_of_fats:
	CALL	NZ, error
	; calculate FAT begin LBA
	LD	DE, (sdcard_block_buffer+volumeid_reserved_sectors)
	LD	BC, 0
	LD	HL, (sdcard_current_block_address) ; parition begin LBA
	ADD	HL, DE
	LD	(fat32_fat_begin_lba), HL
	LD	HL, (sdcard_current_block_address+2) ; parition begin LBA
	ADC	HL, BC
	LD	(fat32_fat_begin_lba+2), HL
	; calculate cluster begin LBA
	LD	DE, (sdcard_block_buffer+volumeid_sectors_per_fat)
	LD	BC, (sdcard_block_buffer+volumeid_sectors_per_fat+2)
	LD	(fat32_fat_number_of_sectors), DE
	LD	(fat32_fat_number_of_sectors+2), BC
	SLA	E ; BCDE <- 2*sectors_per_fat
	RL	D
	RL	C
	RL	B
	LD	HL, (fat32_fat_begin_lba)
	ADD	HL, DE
	LD	(fat32_clusters_begin_lba), HL
	LD	HL, (fat32_fat_begin_lba+2)
	ADC	HL, BC
	LD	(fat32_clusters_begin_lba+2), HL
	; determine cluster size
	LD	A, (sdcard_block_buffer+volumeid_sectors_per_cluster)
	LD	(fat32_sectors_per_cluster), A
	; open root directory
	LD	HL, (sdcard_block_buffer+volumeid_rootdir_first_cluster)
	LD	(fat32_working_directory+chain_first_cluster), HL
	LD	HL, (sdcard_block_buffer+volumeid_rootdir_first_cluster+2)
	LD	(fat32_working_directory+chain_first_cluster+2), HL
	RET

fat32_chain_IX_get_byte_A:
	LD	L, (IX+chain_lba_current_sector+0)
	LD	H, (IX+chain_lba_current_sector+1)
	LD	E, (IX+chain_lba_current_sector+2)
	LD	D, (IX+chain_lba_current_sector+3)
	CALL	sdcard_read_block_DEHL_lazy
	; get sector relative byte address
	LD	L, (IX+stream_position)
	LD	A, (IX+stream_position+1)
	AND	A, $01
	LD	H, A
	; extract byte from sector
	LD	DE, sdcard_block_buffer
	ADD	HL, DE
	LD	A, (HL)
	PUSH	AF
	CALL	fat32_chain_IX_next_byte
	POP	AF
	RET

fat32_chain_IX_put_byte_A:
	PUSH	AF
	LD	L, (IX+chain_lba_current_sector+0)
	LD	H, (IX+chain_lba_current_sector+1)
	LD	E, (IX+chain_lba_current_sector+2)
	LD	D, (IX+chain_lba_current_sector+3)
	CALL	sdcard_read_block_DEHL_lazy
	; get sector relative byte address
	LD	L, (IX+stream_position)
	LD	A, (IX+stream_position+1)
	AND	A, $01
	LD	H, A
	; write byte in sector
	LD	DE, sdcard_block_buffer
	ADD	HL, DE
	POP	AF
	LD	(HL), A
	LD	A, 1
	LD	(sdcard_current_block_dirty), A
	CALL	fat32_chain_IX_next_byte
	RET

fat32_chain_IX_skip_bytes_BC:
	PUSH	BC
	CALL	fat32_chain_IX_next_byte
	POP	BC
	DEC	BC
	LD	A, B
	OR	A, C
	JR	NZ, fat32_chain_IX_skip_bytes_BC
	RET

fat32_chain_IX_next_byte:
	; advance stream to next byte
	LD	L, (IX+stream_position+0)
	LD	H, (IX+stream_position+1)
	LD	E, (IX+stream_position+2)
	LD	D, (IX+stream_position+3)
	LD	BC, 1 ; DEHL += 1
	ADD	HL, BC
	EX	DE, HL
	LD	C, 0
	ADC	HL, BC
	EX	DE, HL
	LD	(IX+stream_position+0), L
	LD	(IX+stream_position+1), H
	LD	(IX+stream_position+2), E
	LD	(IX+stream_position+3), D
	; detect end of sector
	LD	A, H
	AND	A, $01
	OR	A, L
	RET	NZ
	; check if sectors remain in current cluster
	DEC	(IX+chain_sectors_remaining_in_current_cluster)
	JR	Z, fat32_chain_IX_next_byte_next_cluster
	; next sector in current cluster
	LD	L, (IX+chain_lba_current_sector+0)
	LD	H, (IX+chain_lba_current_sector+1)
	LD	E, (IX+chain_lba_current_sector+2)
	LD	D, (IX+chain_lba_current_sector+3)
	LD	BC, 1 ; DEHL += 1
	ADD	HL, BC
	EX	DE, HL
	LD	C, 0
	ADC	HL, BC
	EX	DE, HL
	LD	(IX+chain_lba_current_sector+0), L
	LD	(IX+chain_lba_current_sector+1), H
	LD	(IX+chain_lba_current_sector+2), E
	LD	(IX+chain_lba_current_sector+3), D
	RET
fat32_chain_IX_next_byte_next_cluster:
	CALL	fat32_chain_IX_lookup_next_cluster
	LD	L, (IX+chain_current_cluster)
	LD	H, (IX+chain_current_cluster+1)
	LD	E, (IX+chain_current_cluster+2)
	LD	D, (IX+chain_current_cluster+3)
	LD	BC, -2 ; DEHL <- cluster number - 2
	ADD	HL, BC
	EX	DE, HL
	LD	BC, $FFFF
	ADC	HL, BC
	EX	DE, HL
	LD	A, (fat32_sectors_per_cluster)
	fat32_chain_IX_next_byte_next_cluster_calc_LBA_mult_loop:
	SRL	A ; DEHL *= sectors per cluster (power of 2)
	JR	Z, fat32_chain_IX_next_byte_next_cluster_calc_LBA_mult_done
	SLA	L
	RL	H
	RL	E
	RL	D
	JR	fat32_chain_IX_next_byte_next_cluster_calc_LBA_mult_loop
	fat32_chain_IX_next_byte_next_cluster_calc_LBA_mult_done:
	LD	BC, (fat32_clusters_begin_lba)
	ADD	HL, BC ; lba = DEHL + fat32_clusters_begin_lba
	LD	(IX+chain_lba_current_sector+0), L
	LD	(IX+chain_lba_current_sector+1), H
	EX	DE, HL
	LD	BC, (fat32_clusters_begin_lba+2)
	ADC	HL, BC
	LD	(IX+chain_lba_current_sector+2), L
	LD	(IX+chain_lba_current_sector+3), H
	; all sectors remaining
	LD	A, (fat32_sectors_per_cluster)
	LD	(IX+chain_sectors_remaining_in_current_cluster), A
	RET

fat32_chain_IX_lookup_next_cluster:
	LD	A, (IX+chain_current_cluster)
	LD	L, (IX+chain_current_cluster+1)
	LD	H, (IX+chain_current_cluster+2)
	LD	E, (IX+chain_current_cluster+3)
	; bit 31-7 = LBA relative to fat_begin
	LD	D, 0
	SLA	A
	RL	L
	RL	H
	RL	E
	RL	D
	LD	BC, (fat32_fat_begin_lba)
	ADD	HL, BC
	EX	DE, HL
	LD	BC, (fat32_fat_begin_lba+2)
	ADC	HL, BC
	EX	DE, HL
	CALL	sdcard_read_block_DEHL_lazy
	; bit  6-0 = index of 32bit integer in sector
	LD	A, (IX+chain_current_cluster)
	AND	A, $7F
	LD	L, A
	LD	H, 0
	ADD	HL, HL
	ADD	HL, HL
	LD	BC, sdcard_block_buffer
	ADD	HL, BC
	LD	A, $FF
	LD	B, (HL)
	AND	A, B
	LD	(IX+chain_current_cluster+0), B
	INC	HL
	LD	B, (HL)
	AND	A, B
	LD	(IX+chain_current_cluster+1), B
	INC	HL
	LD	B, (HL)
	AND	A, B
	LD	(IX+chain_current_cluster+2), B
	INC	HL
	LD	B, (HL)
	AND	A, B
	LD	(IX+chain_current_cluster+3), B
	CP	A, $FF
fat32_chain_IX_lookup_next_cluster_error_end_of_chain:
	CALL	Z, error
	RET

fat32_chain_IX_seek_BCDE:
	LD	(IX+stream_position+0), E
	LD	(IX+stream_position+1), D
	LD	(IX+stream_position+2), C
	LD	(IX+stream_position+3), B
	; current cluster <- first cluster
	LD	A, (IX+chain_first_cluster)
	LD	(IX+chain_current_cluster), A
	LD	A, (IX+chain_first_cluster+1)
	LD	(IX+chain_current_cluster+1), A
	LD	A, (IX+chain_first_cluster+2)
	LD	(IX+chain_current_cluster+2), A
	LD	A, (IX+chain_first_cluster+3)
	LD	(IX+chain_current_cluster+3), A
fat32_chain_IX_seek_BCDE_cluster_loop:
	; calculate cluster size in bytes
	LD	A, (fat32_sectors_per_cluster)
	LD	H, A
	XOR	A, A
	LD	L, A
	SLA	H ; AHL <- sectors per cluster * 512
	ADC	A, 0 ; note: carry cleared after this
	; subtract cluster size from seek address
	EX	DE, HL ; BCDE -= AHL
	SBC	HL, DE
	EX	DE, HL
	LD	HL, BC
	LD	C, A
	LD	B, 0
	SBC	HL, BC
	LD	BC, HL
	JR	C, fat32_chain_IX_seek_BCDE_cluster_found
	; look up next cluster in FAT
	PUSH	DE
	PUSH	BC
	CALL	fat32_chain_IX_lookup_next_cluster
	POP	BC
	POP	DE
	; repeat
	JR	fat32_chain_IX_seek_BCDE_cluster_loop
fat32_chain_IX_seek_BCDE_cluster_found:
	; add custer size again to get relative position
	LD	A, (fat32_sectors_per_cluster)
	LD	H, A
	XOR	A, A
	LD	L, A
	SLA	H ; AHL <- sectors per cluster * 512
	ADC	A, 0
	EX	DE, HL ; BCDE += AHL
	ADD	HL, DE
	EX	DE, HL
	LD	HL, BC
	LD	C, A
	LD	B, 0
	ADC	HL, BC
	LD	BC, HL
	; since clusters are max 64kB in size, BC should be 0 now
	LD	A, B
	OR	A, C
fat32_init_error_invalid_cluster_size:
	CALL	NZ, error
	; calculate LBA for 1st sector of current cluster
	PUSH	DE
	LD	L, (IX+chain_current_cluster)
	LD	H, (IX+chain_current_cluster+1)
	LD	E, (IX+chain_current_cluster+2)
	LD	D, (IX+chain_current_cluster+3)
	;ld	a, 'c'
	;call	debug_io_print_character_A
	;ld	a, d
	;call	debug_io_print_hex_byte_A
	;ld	a, e
	;call	debug_io_print_hex_byte_A
	;ld	a, h
	;call	debug_io_print_hex_byte_A
	;ld	a, l
	;call	debug_io_print_hex_byte_A
	;ld	a, 10 ; \n
	;call	debug_io_print_character_A
	LD	BC, -2 ; DEHL <- cluster number - 2
	ADD	HL, BC
	EX	DE, HL
	LD	BC, $FFFF
	ADC	HL, BC
	EX	DE, HL
	LD	A, (fat32_sectors_per_cluster)
fat32_chain_IX_seek_BCDE_calc_LBA_mult_loop:
	SRL	A ; DEHL *= sectors per cluster (power of 2)
	JR	Z, fat32_chain_IX_seek_BCDE_calc_LBA_mult_done
	SLA	L
	RL	H
	RL	E
	RL	D
	JR	fat32_chain_IX_seek_BCDE_calc_LBA_mult_loop
fat32_chain_IX_seek_BCDE_calc_LBA_mult_done:
	LD	BC, (fat32_clusters_begin_lba)
	ADD	HL, BC ; DEHL += fat32_clusters_begin_lba
	EX	DE, HL
	LD	BC, (fat32_clusters_begin_lba+2)
	ADC	HL, BC
	EX	DE, HL
	; calculate correct sector within cluster
	POP	BC ; cluster relative byte address
	LD	C, B
	LD	B, 0
	SRL	C ; divided by 512 now
	LD	A, C ; needed later
	ADD	HL, BC
	EX	DE, HL
	LD	C, 0 ; B is already 0
	ADC	HL, BC
	EX	DE, HL
	LD	(IX+chain_lba_current_sector+0), L
	LD	(IX+chain_lba_current_sector+1), H
	LD	(IX+chain_lba_current_sector+2), E
	LD	(IX+chain_lba_current_sector+3), D
	; sectors remaining <- sectors per cluster - sector in current cluster
	LD	B, A ; value saved above
	LD	A, (fat32_sectors_per_cluster)
	SUB	A, B
	LD	(IX+chain_sectors_remaining_in_current_cluster), A
	RET

section objects_mutable
fat32_working_directory:
defw	fat32_chain_IX_get_byte_A ;stream_get_byte_A
defw	fat32_chain_IX_put_byte_A ;stream_put_byte_A
defw	stream_IX_read_block_DE_len_BC_bytewise ;stream_read_block_DE_len_BC
defw	stream_IX_write_block_DE_len_BC_bytewise ;stream_write_block_DE_len_BC
defw	fat32_chain_IX_skip_bytes_BC ;stream_skip_bytes_BC
defw	0, 0	;stream_position
defw	-1, -1	;stream_size
defw	fat32_chain_IX_seek_BCDE ;stream_seek_BCDE
defw	0, 0	;chain_first_cluster
defw	0, 0	;chain_current_cluster
defw	0, 0	;chain_lba_current_sector
defb	0	;chain_sectors_remaining_in_current_cluster
defs	32	;directory_current_entry_buffer ds.b 32

section ram_uninitialized
fat32_fat_begin_lba:
defs	4
fat32_fat_number_of_sectors:
defs	4
fat32_clusters_begin_lba:
defs	4
fat32_sectors_per_cluster:
defs	1
