Noah1989/loopmicro/software/new-rom/lorem_ipsum.asm

public lorem_ipsum

section strings
defb	0
lorem_ipsum:
defb	10
defb	"Lorem ipsum dolor sit amet, consectetur adipiscing", 10
defb	"elit. Cras sagittis vestibulum dui sed pellentesque.", 10
defb	"Donec sit amet semper lectus. Vestibulum dapibus", 10
defb	"metus consectetur aliquet viverra. Pellentesque", 10
defb	"habitant morbi tristique senectus et netus et", 10
defb	"malesuada fames ac turpis egestas. Morbi tristique", 10
defb	"augue leo, eget dictum neque imperdiet non. Sed a", 10
defb	"risus dapibus, rutrum velit in, commodo arcu. Ut", 10
defb	"suscipit posuere ante ac vulputate. Quisque dapibus", 10
defb	"faucibus quam eget tempus. Aliquam et neque odio.", 10
defb	10
defb	"Praesent dignissim metus nunc, euismod scelerisque", 10
defb	"purus hendrerit ultrices. In tempor at arcu et", 10
defb	"posuere. Ut tempor sem tempor pellentesque faucibus.", 10
defb	"Mauris vulputate magna sit amet neque malesuada", 10
defb	"condimentum. Pellentesque condimentum elit volutpat", 10
defb	"vehicula rutrum. Quisque sit amet mauris congue,", 10
defb	"placerat purus ac, porta turpis. Nullam at dictum", 10
defb	"nunc, finibus commodo eros.", 10
defb	10
defb	"Morbi quis arcu accumsan, dignissim dolor id,", 10
defb	"sollicitudin enim. Vestibulum gravida, ex ut dapibus", 10
defb	"porta, justo lectus varius risus, at consectetur", 10
defb	"quam dolor at quam. Interdum et malesuada fames ac", 10
defb	"ante ipsum primis in faucibus. Etiam rutrum pharetra", 10
defb	"commodo. Ut quis viverra turpis. Integer pharetra", 10
defb	"varius efficitur. Sed vestibulum augue in ante", 10
defb	"consectetur rutrum. Nunc luctus enim arcu, blandit", 10
defb	"rhoncus orci tempor vitae. Cras tincidunt est a elit", 10
defb	"scelerisque commodo. Suspendisse potenti. Sed", 10
defb	"pulvinar, velit eu dictum gravida, tortor dui", 10
defb	"blandit odio, eget malesuada tortor mauris et ipsum.", 10
defb	"Donec orci purus, pellentesque sed purus ultrices,", 10
defb	"suscipit aliquam lorem. Nullam sagittis aliquet", 10
defb	"diam, eget auctor dui tempus eget.", 10
defb	10
defb	"Ut magna nulla, cursus non convallis ut, pharetra in", 10
defb	"velit. Suspendisse lobortis libero id scelerisque", 10
defb	"placerat. Mauris in dolor fermentum, iaculis arcu", 10
defb	"sed, bibendum quam. Vivamus ultrices iaculis metus,", 10
defb	"et tempus arcu. Duis sed blandit erat. Etiam et leo", 10
defb	"sed ex ultricies fermentum. Integer scelerisque", 10
defb	"pellentesque nunc ac molestie. Lorem ipsum dolor sit", 10
defb	"amet, consectetur adipiscing elit. Suspendisse", 10
defb	"potenti. Curabitur interdum, nisl in rutrum semper,", 10
defb	"nibh augue imperdiet lacus, sit amet aliquam velit", 10
defb	"tellus posuere massa. Ut sit amet elit eleifend,", 10
defb	"luctus neque vel, euismod elit.", 10
defb	10
defb	"Phasellus finibus ipsum quam, vitae ullamcorper", 10
defb	"sapien gravida vitae. Suspendisse ornare mollis", 10
defb	"elit, volutpat mattis augue malesuada sed. Nam", 10
defb	"scelerisque sagittis risus, eu consequat nibh", 10
defb	"sodales quis. In dignissim risus vel eros vehicula", 10
defb	"porta. Proin ut facilisis purus, eget iaculis quam.", 10
defb	"Mauris sed urna tristique sapien faucibus vestibulum", 10
defb	"ac et enim. Maecenas lacus eros, semper ac accumsan", 10
defb	"a, faucibus vel tellus. Sed eu lacinia urna.", 10
defb	"Vestibulum sit amet mi convallis, feugiat orci nec,", 10
defb	"mattis augue. Nulla vel lacus non ligula sodales", 10
defb	"facilisis. Nam a neque odio. Mauris efficitur tempus", 10
defb	"nisi ut sollicitudin. Cras elementum, sem eu", 10
defb	"tincidunt semper, nibh leo lacinia eros, ut molestie", 10
defb	"mauris nulla nec nibh. Suspendisse lacinia nunc id", 10
defb	"suscipit blandit. Nullam ut facilisis dui. ", 10
defb	10
defb	0
