Noah1989/loopmicro/emulator/led.hpp

#ifndef LED_HPP
#define LED_HPP

#include <string>
#include <SDL2/SDL.h>
#include <SDL2/SDL_image.h>

#include "actor.hpp"
#include "signal.hpp"
#include "label.hpp"

class Led : public Actor
{
    public:
        Led(SDL_Renderer *renderer, SDL_Point pos, const char *labelText,
            const std::string &image_name, Signal *input, bool inverted = false);

        void tick();
        bool render(int layer);

    private:
        SDL_Rect     rect;
        SDL_Texture *baseImage;
        SDL_Texture *lightImage;
        Signal      *input;
        Label       *label;
        bool        inverted;
        int         valueSum;
        int         valueCount;
};

#endif // LED_HPP
