Noah1989/loopmicro/software/new-rom/math.asm

public multiply_DE_A_result_HL_zero_B

multiply_DE_A_result_HL_zero_B:
;Inputs:
;     DE and A are factors
;Outputs:
;     A is not changed
;     B is 0
;     C is not changed
;     DE is not changed
;     HL is the product
;Time:
;     342+6x
;
     ld b,8          ;7           7
     ld hl,0         ;10         10
       add hl,hl     ;11*8       88
       rlca          ;4*8        32
       jr nc,$+3     ;(12|18)*8  96+6x
         add hl,de   ;--         --
       djnz $-5      ;13*7+8     99
     ret             ;10         10
